DARKMOONlite/Algae_Panel/CAD/Interior Mount for Electrical Box/schemtic .png

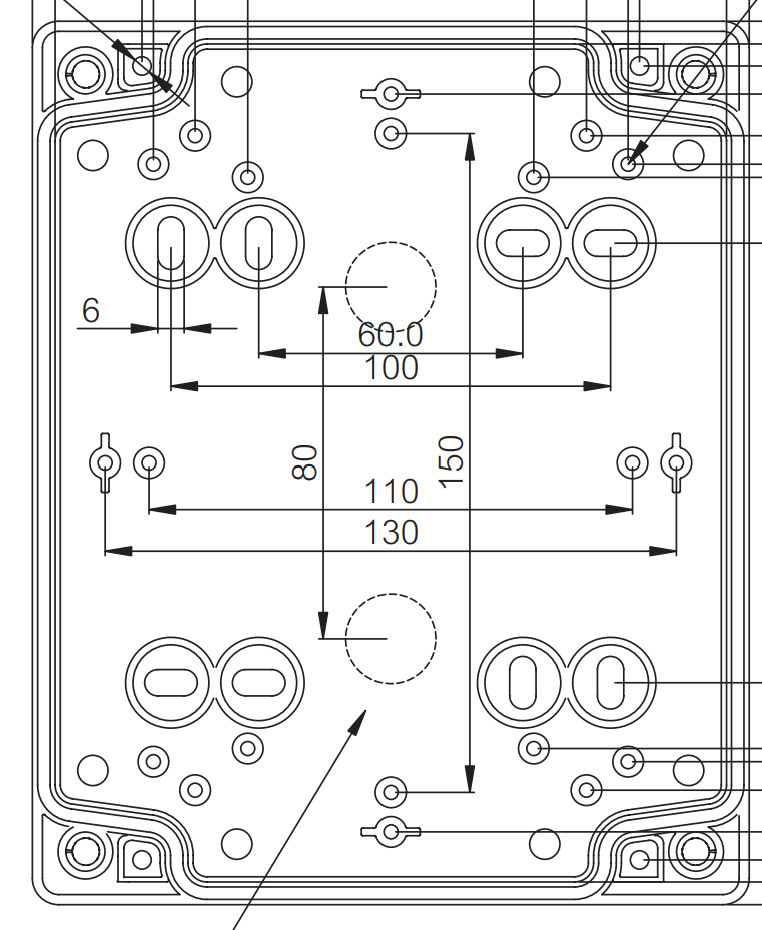
CAD/Interior Mount for Electrical Box/schemtic .png
