DARKMOONlite/Algae_Panel/CAD/Interior Mount for Electrical Box/two-way screw terminal.png

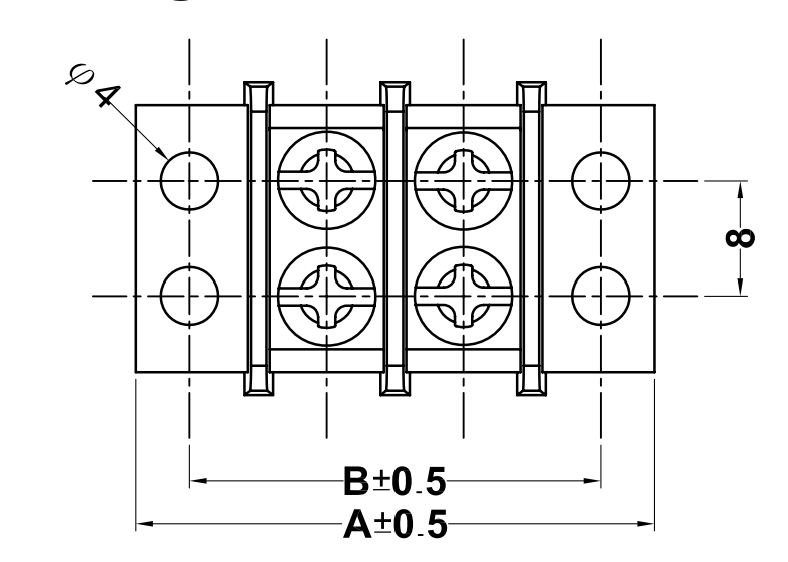
CAD/Interior Mount for Electrical Box/two-way screw terminal.png
