DARKMOONlite/Algae_Panel/CAD/Plumbing/7. 15mm Brass Solenoid Valve (ADA996)/2017 GrabCAD/Capturar.JPG

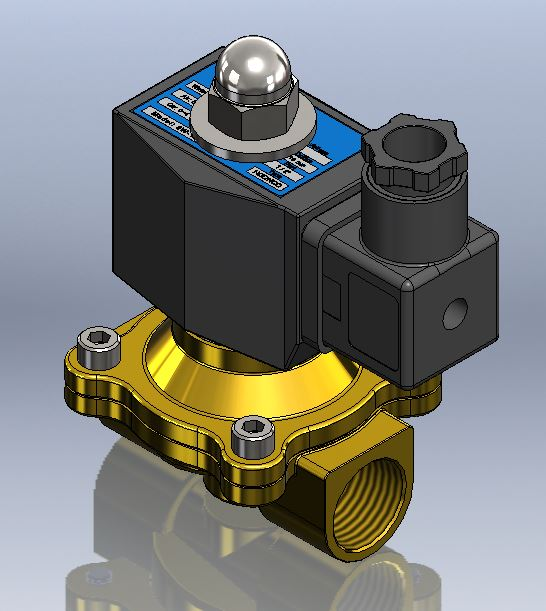
CAD/Plumbing/7. 15mm Brass Solenoid Valve (ADA996)/2017 GrabCAD/Capturar.JPG
