DARKMOONlite/Algae_Panel/CAD/Plumbing/7. 15mm Brass Solenoid Valve (ADA996)/2021 GrabCAD/kp2s-160-15b-Solenoid Valve.jpg

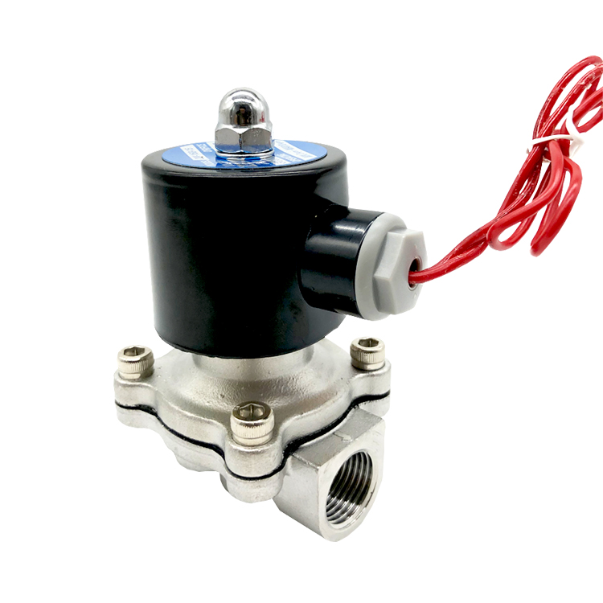
CAD/Plumbing/7. 15mm Brass Solenoid Valve (ADA996)/2021 GrabCAD/kp2s-160-15b-Solenoid Valve.jpg
