DARKMOONlite/Algae_Panel/CAD/GrabCad Models of Electricals/4 Channel No Name Relay Parts/Relay - 4 Ch - 5v Montaj.SLDASM

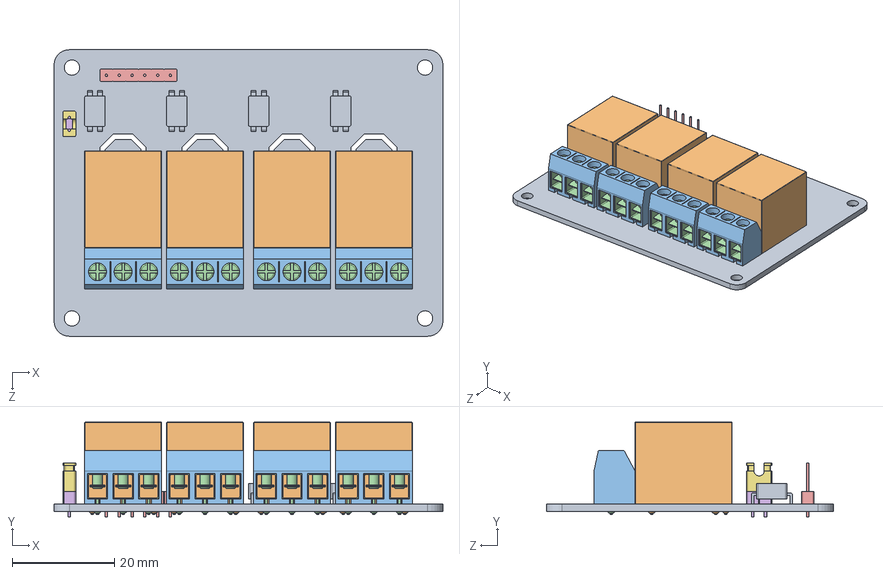
[picture p22: CAD file, 2023-05-31]
CAD/GrabCad Models of Electricals/4 Channel No Name Relay Parts/Relay - 4 Ch - 5v Montaj.SLDASM
76.0 x 18.5 x 56.0 mm
4 Ch - 5v Relay Board
Relay Body x 4
Clamp Body x 4
Metal Clamp Part x 12
6 Header
2 Header
Jumper
