DARKMOONlite/Algae_Panel/CAD/GrabCad Models of Electricals/4 Channel No Name Relay Parts/Metal Clamp Part.SLDPRT

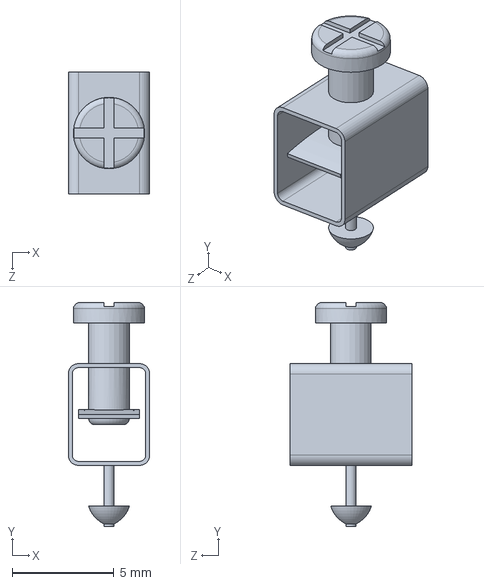
[picture p23: CAD file, 2023-05-31]
CAD/GrabCad Models of Electricals/4 Channel No Name Relay Parts/Metal Clamp Part.SLDPRT
4.00 x 11.0 x 6.00 mm
