DARKMOONlite/Algae_Panel/CAD/GrabCad Models of Electricals/arduinoMega.SLDPRT

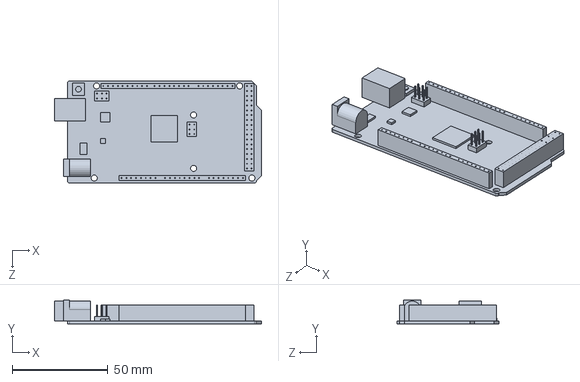
[picture p24: CAD file, 2023-05-31]
CAD/GrabCad Models of Electricals/arduinoMega.SLDPRT
108.3 x 12.5 x 53.3 mm
