DARKMOONlite/Algae_Panel/Software/Algae Project/include/AlgaePanelRemote.hpp

/**
 * @file AlgaePanelRemote.hpp
 * @author Sebastian Schroder
 * @brief Defines all IR codes produced by the relacent IR remote
 * new buttons can be added by adding them to this list and adding a relavent function in the 
 * @version 0.1
 * @date 2023-06-02
 * 
 * @copyright Copyright (c) 2023
 * 
 */
#ifndef ALGAE_PANEL_REMOTE_CODES_H
#define ALGAE_PANEL_REMOTE_CODES_H


#define IRREMOTE_DOWN 97
#define IRREMOTE_UP 96
#define IRREMOTE_LEFT 101
#define IRREMOTE_RIGHT 98
#define IRREMOTE_CENTRE 104
#define IRREMOTE_OFF 2
#define IRREMOTE_MENU 26
 

#define IRREMOTE_RED 108

#define IRREMOTE_BLUE 22

#define IRREMOTE_GREEN 20

#define IRREMOTE_YELLOW 21
#endif 
