DARKMOONlite/Algae_Panel/Software/Algae Project/src/global_variables.cpp

/**
 * @file global_variables.cpp
 * @author Sebastian Schroder
 * @brief This contains the definitions of global variables declared in the .h file
 * @version 0.1
 * @date 2023-06-02
 * 
 * @copyright Copyright (c) 2023
 * 
 */
#include <global_variables.h>

    //-----------------------------     Global Variables ---------------------------------------
int Temp1[Cyclic_Array_Size],Temp2[Cyclic_Array_Size];
int SonarDist1[Cyclic_Array_Size], IRDist2[Cyclic_Array_Size];
uint8_t Cyclic_Array_Index=0;
int Temp1Average=0, Temp2Average=0, SonarAverage=0, IRAverage=0;



Control_State PumpState = Control_State::Off, SolanoidState = Control_State::Off;
Control_State prevPumpState = Control_State::Off, prevSolanoidState = Control_State::Off;
    //-----------------------------     Global Objects Declarations  ----------------------------------
LiquidCrystal_I2C lcd = LiquidCrystal_I2C(0x27,16,2);


    //-----------------------------     EEPROM Variable Definitions  ----------------------------------
EEPROM_Manager rom_manager;
EEPROM_Variable manual_dutycycle(100,1,&rom_manager);
EEPROM_Variable autosave(10,2,&rom_manager);
EEPROM_Variable default_solanoid_state(0,3,&rom_manager);



uint32_t lastStateUpdate=0, lastLCDUpdate=0, lastSensorUpdate=0;
