DARKMOONlite/Algae_Panel/Software/Algae Project/src/functional_tests/lcd_test.cpp

#include <LiquidCrystal.h> // includes the LiquidCrystal Library 
#include <Arduino.h>
LiquidCrystal lcd(2, 3, 4, 5, 6, 7); // Creates an LCD object. Parameters: (rs, enable, d4, d5, d6, d7) 

void setup() { 
 lcd.begin(16,2); // Initializes the interface to the LCD screen, and specifies the dimensions (width and height) of the display } 
}

void loop() { 
    lcd.setCursor(0,1);
    // lcd.print("FooA()    ");
 lcd.print("Arduino"); // Prints "Arduino" on the LCD 
 delay(300); // 3 seconds delay 
 lcd.setCursor(2,1); // Sets the location at which subsequent text written to the LCD will be displayed 
 lcd.print("LCD Tutorial"); 
 delay(300); 
 lcd.clear(); // Clears the display 
 lcd.blink(); //Displays the blinking LCD cursor 
 delay(400); 
 lcd.setCursor(7,1); 
 delay(300); 
 lcd.noBlink(); // Turns off the blinking LCD cursor 
 lcd.cursor(); // Displays an underscore (line) at the position to which the next character will be written 
 delay(400); 
 lcd.noCursor(); // Hides the LCD cursor 
 lcd.clear(); // Clears the LCD screen 
}
